natehorst240-sketch/HoboBalancer/BalancerREF/review/accel.png

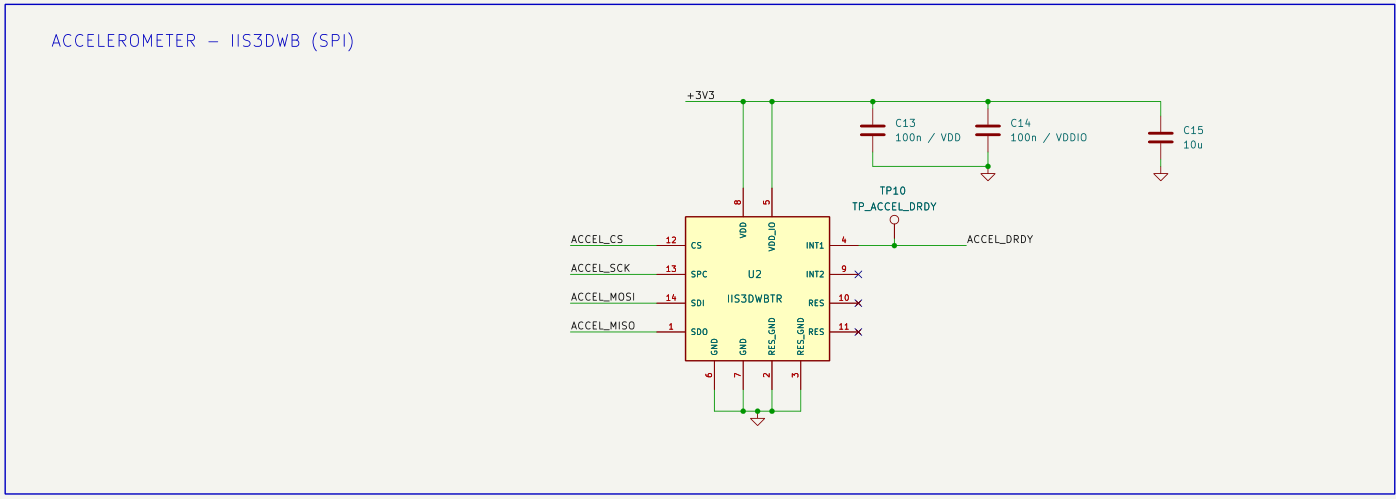
BalancerREF/review/accel.png
