natehorst240-sketch/HoboBalancer/BalancerREF/review/AO3401A-pinout.png

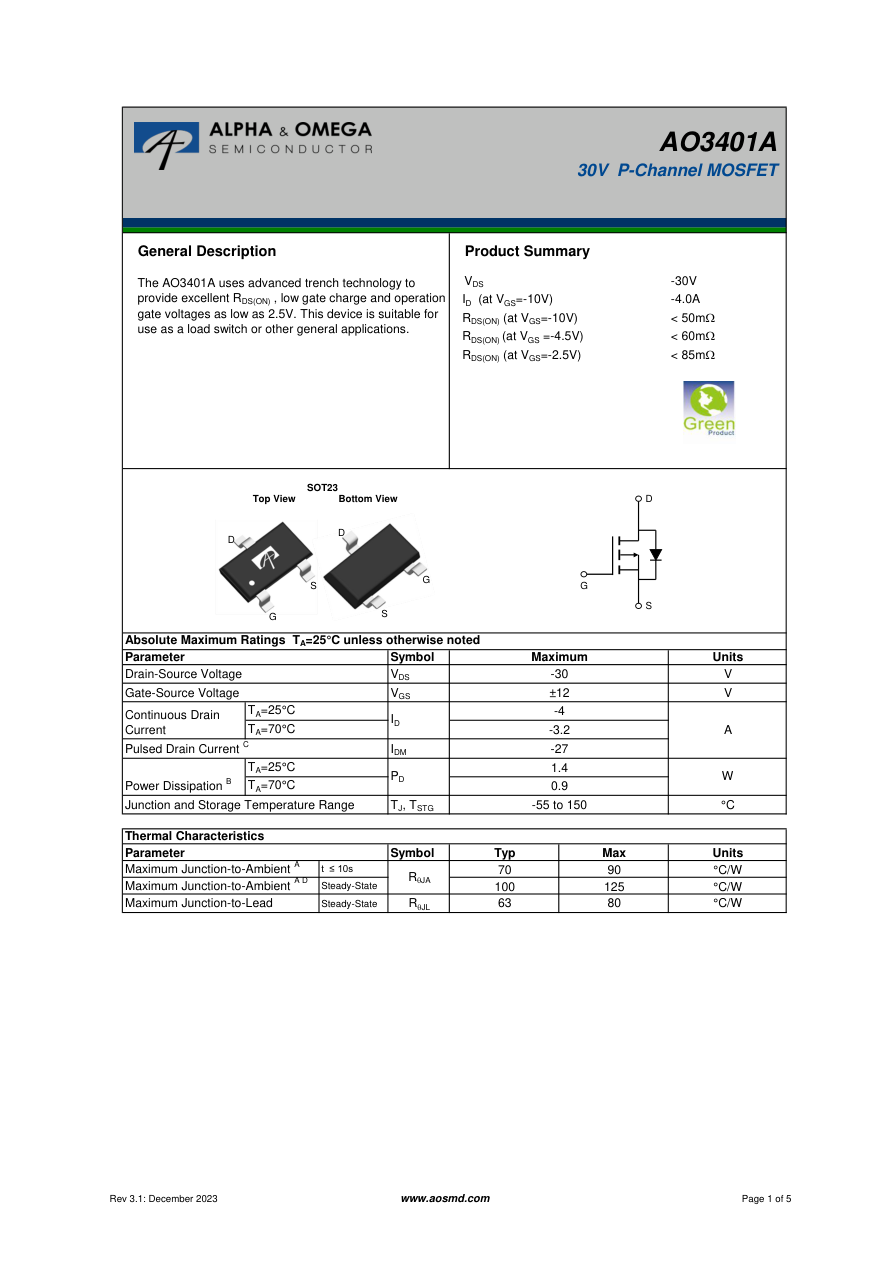
BalancerREF/review/AO3401A-pinout.png
