natehorst240-sketch/HoboBalancer/BalancerREF/review/lm1815-p1.png

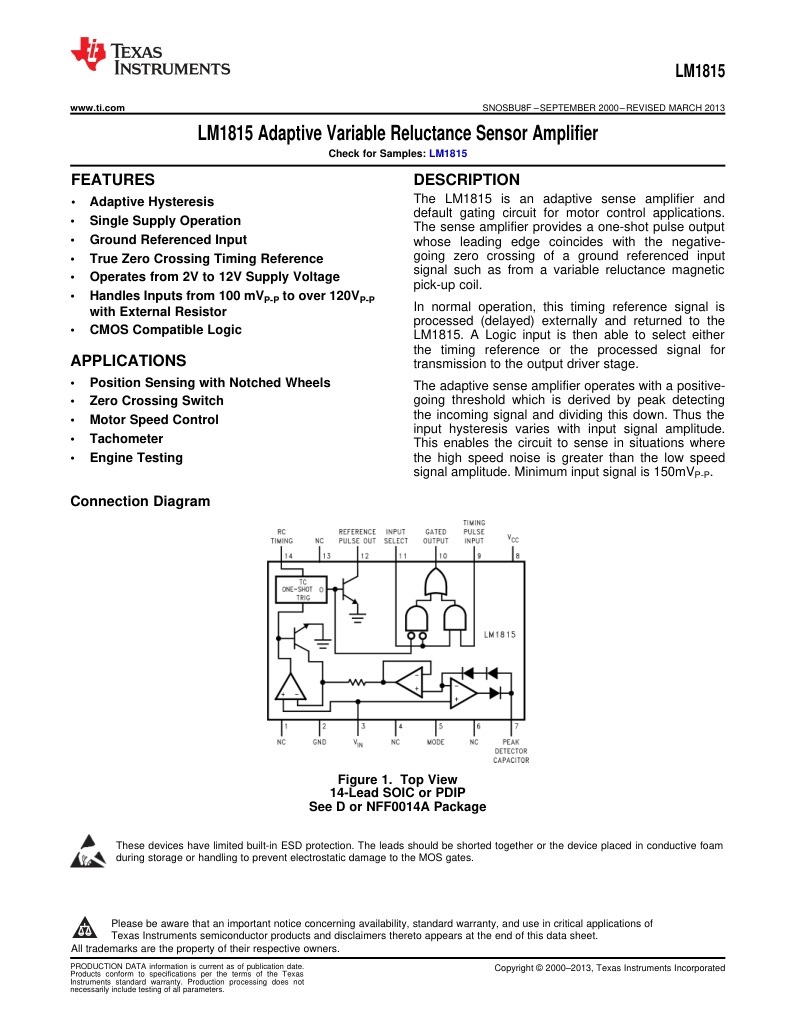
BalancerREF/review/lm1815-p1.png
