natehorst240-sketch/HoboBalancer/BalancerREF/review/lm1815-p6.png

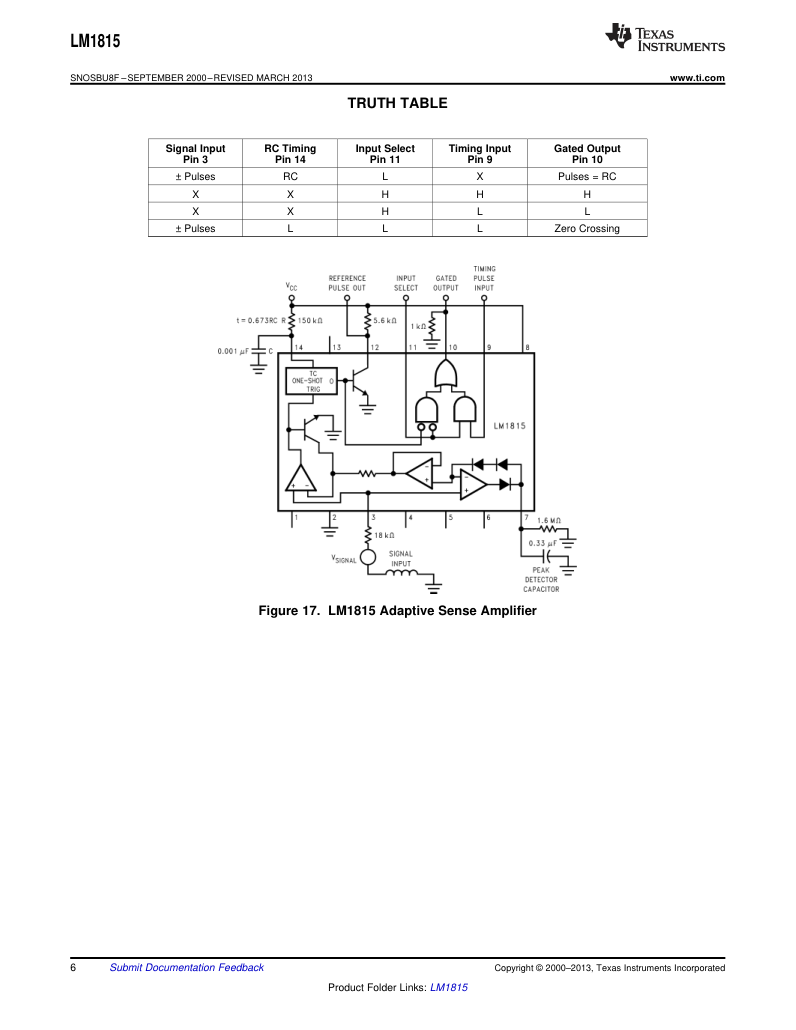
BalancerREF/review/lm1815-p6.png
