natehorst240-sketch/HoboBalancer/BalancerREF/review/mag.png

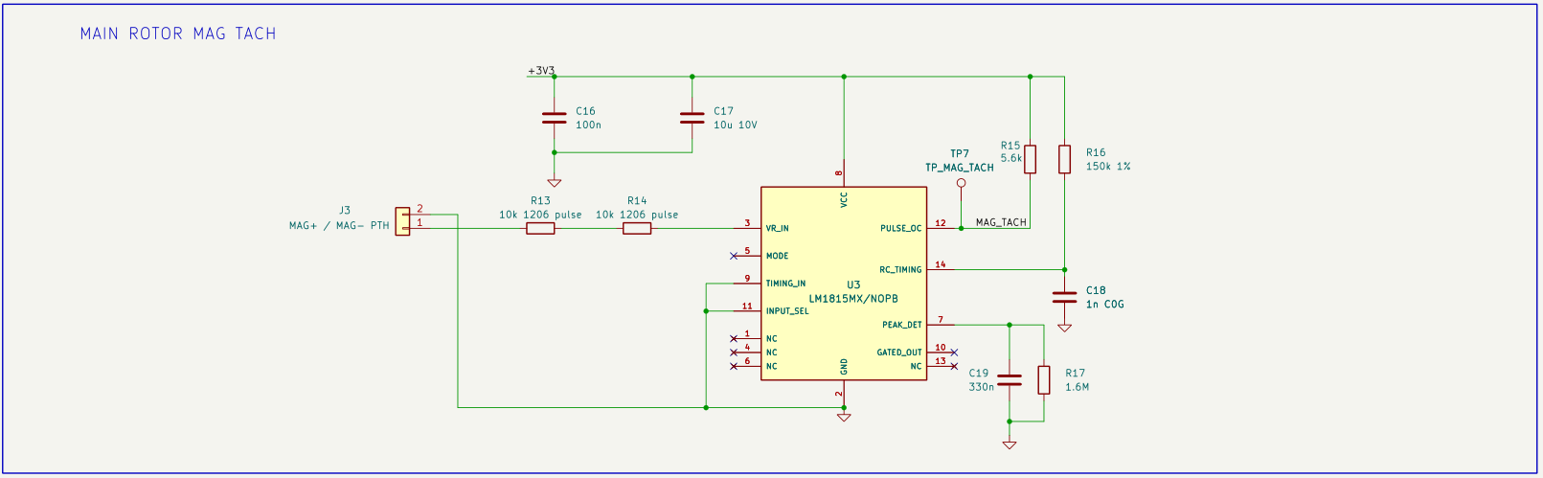
BalancerREF/review/mag.png
