natehorst240-sketch/HoboBalancer/BalancerREF/review/mcu.png

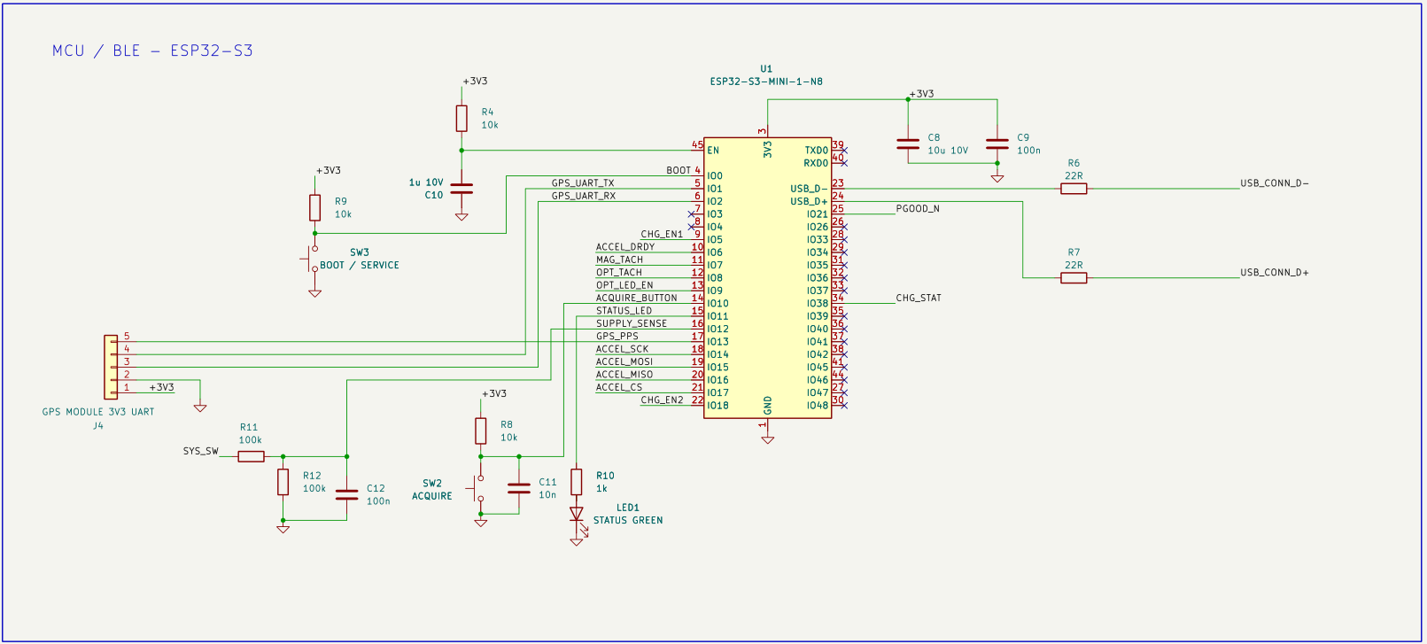
BalancerREF/review/mcu.png
