natehorst240-sketch/HoboBalancer/BalancerREF/review/notes-gps.png

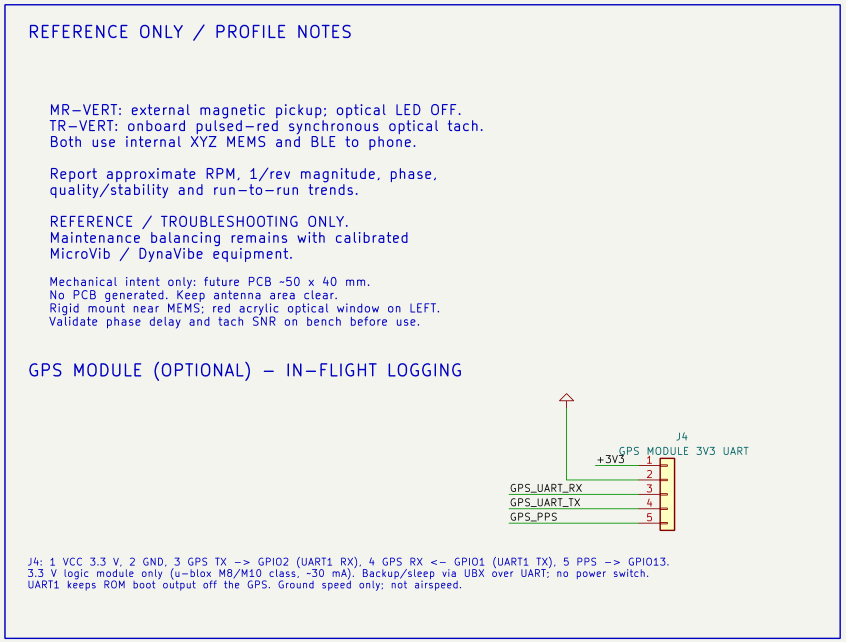
BalancerREF/review/notes-gps.png
