natehorst240-sketch/HoboBalancer/BalancerREF/review/opt-logic.png

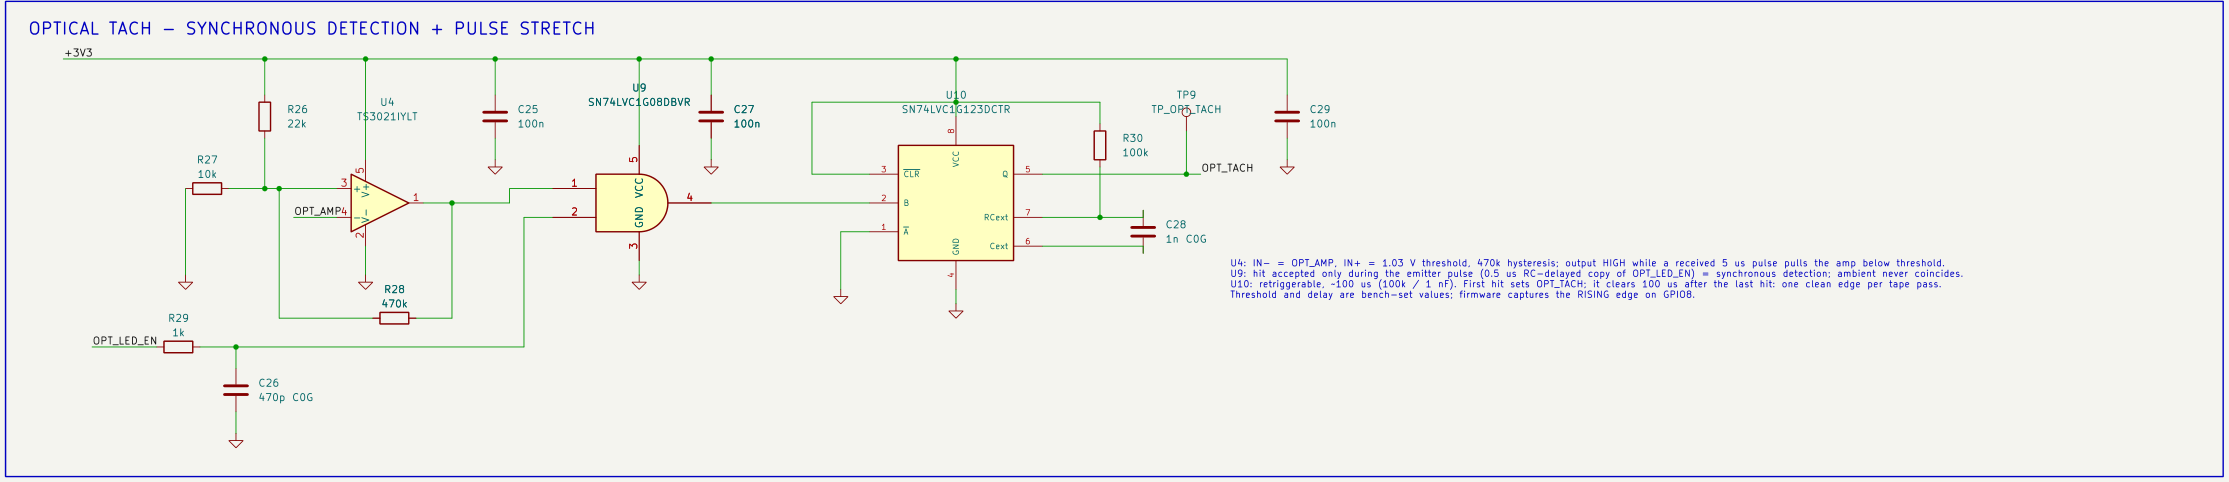
BalancerREF/review/opt-logic.png
