natehorst240-sketch/HoboBalancer/BalancerREF/review/opt.png

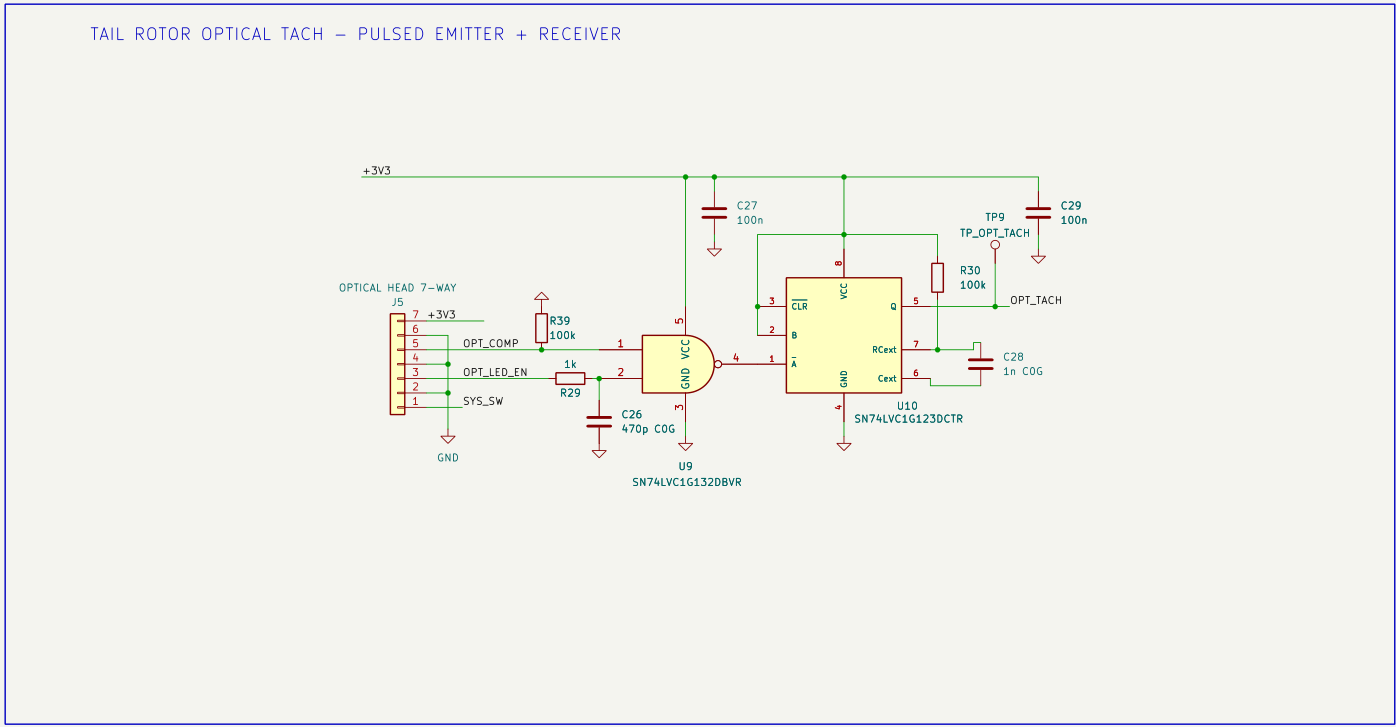
BalancerREF/review/opt.png
