natehorst240-sketch/HoboBalancer/BalancerREF/review/power-sharing.png

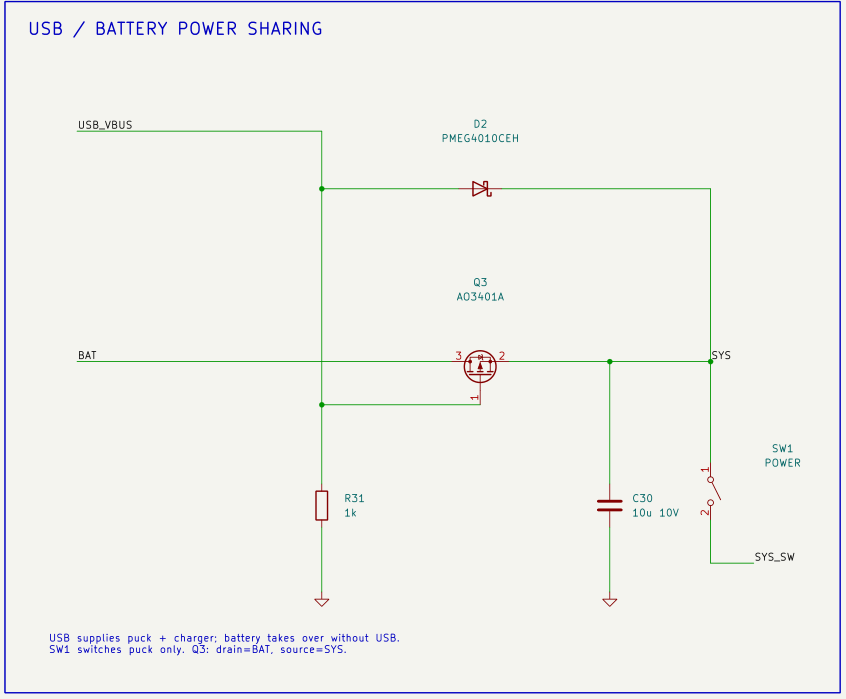
BalancerREF/review/power-sharing.png
