natehorst240-sketch/HoboBalancer/BalancerREF/review/power.png

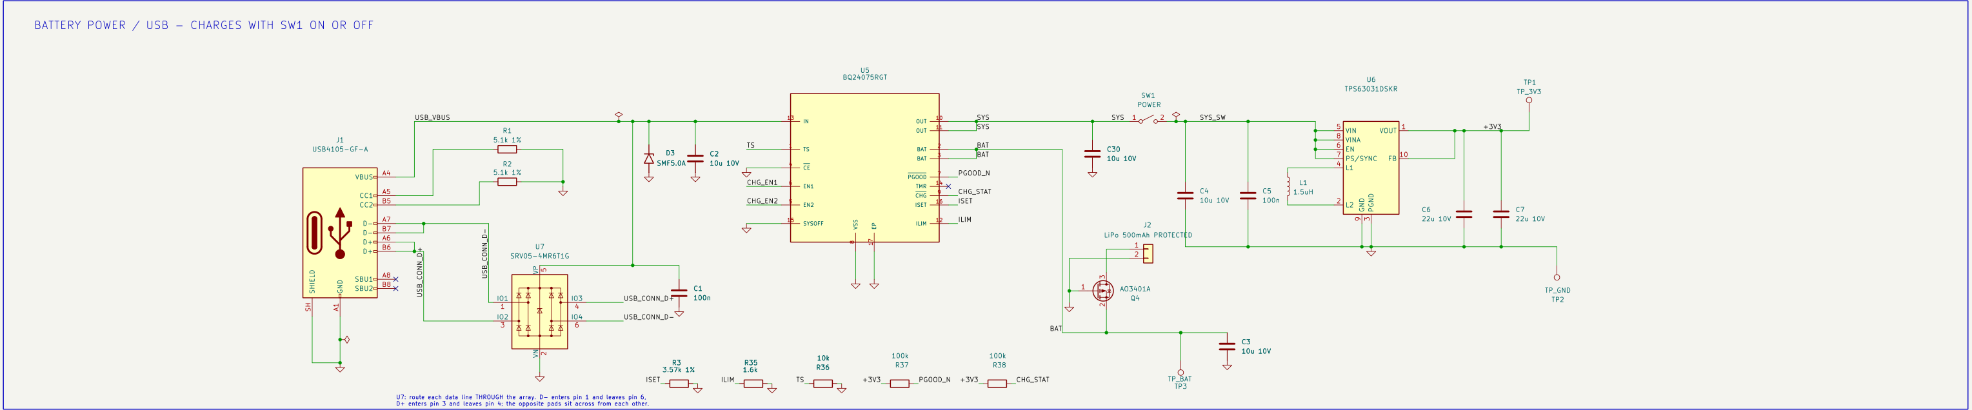
BalancerREF/review/power.png
