natehorst240-sketch/HoboBalancer/BalancerREF/review/reddit/board-head-top.png

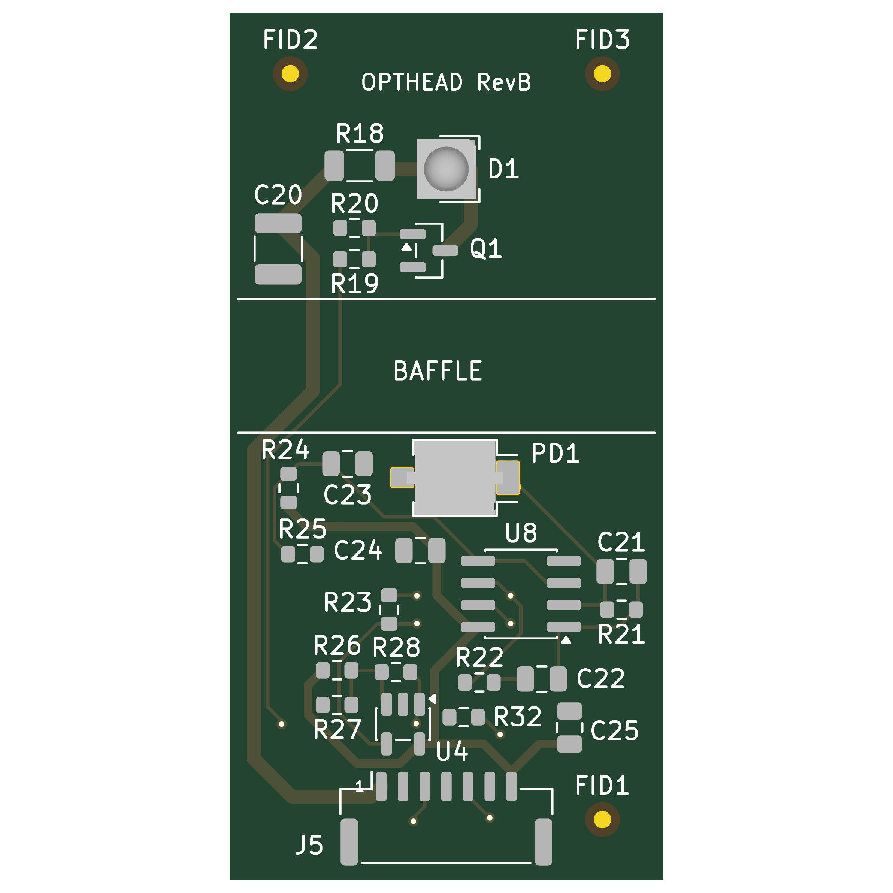
BalancerREF/review/reddit/board-head-top.png
