natehorst240-sketch/HoboBalancer/BalancerREF/review/reddit/board-main-bottom.png

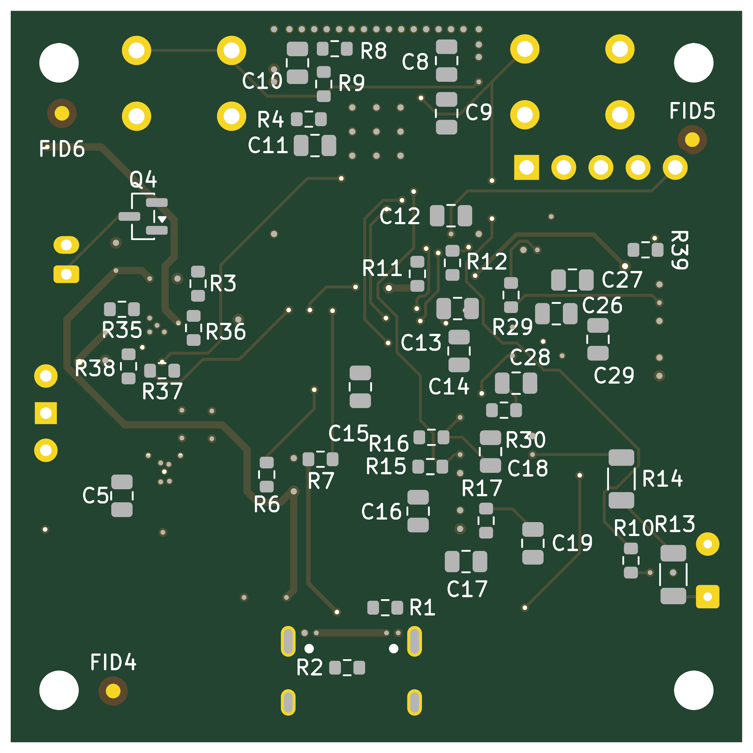
BalancerREF/review/reddit/board-main-bottom.png
