natehorst240-sketch/HoboBalancer/BalancerREF/review/reddit/board-main-top.png

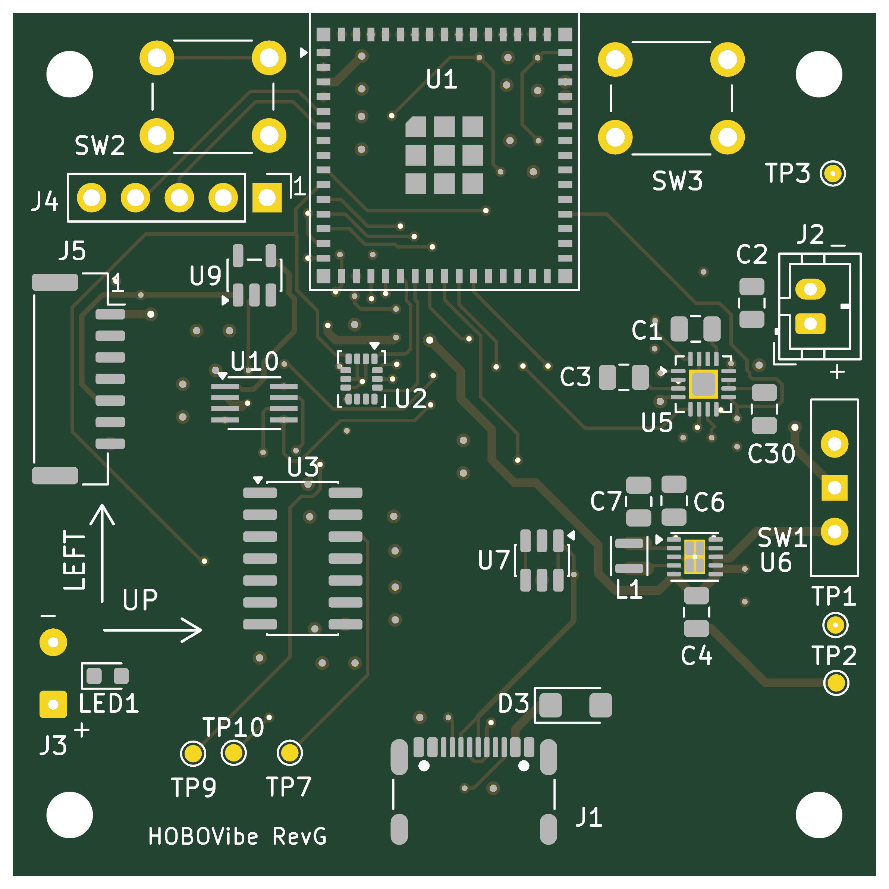
BalancerREF/review/reddit/board-main-top.png
