natehorst240-sketch/HoboBalancer/BalancerREF/review/reg.png

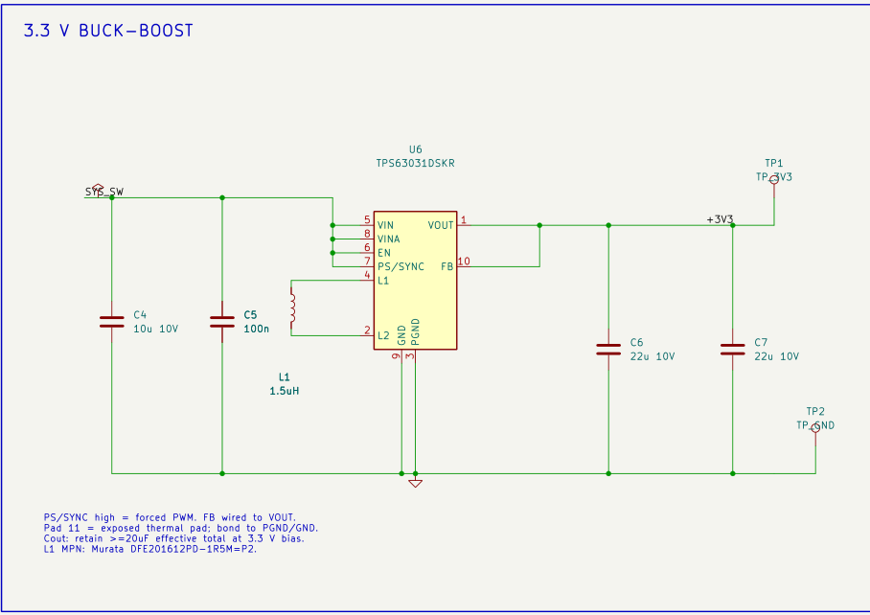
BalancerREF/review/reg.png
