natehorst240-sketch/HoboBalancer/BalancerREF/review/ui.png

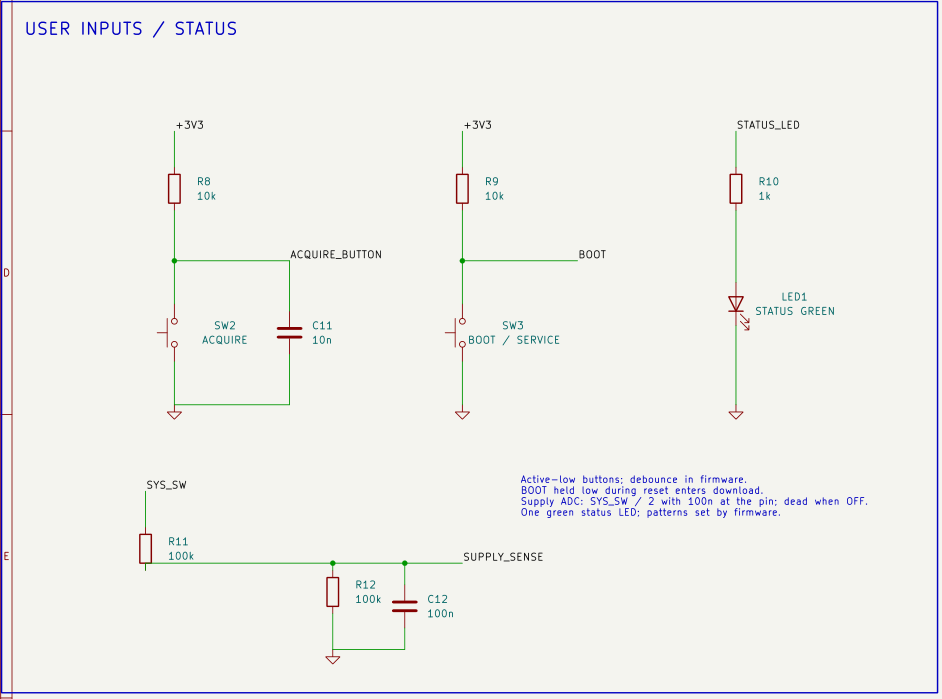
BalancerREF/review/ui.png
