natehorst240-sketch/HoboBalancer/BalancerREF/BalancerREF-Schematic-RevD.pdf

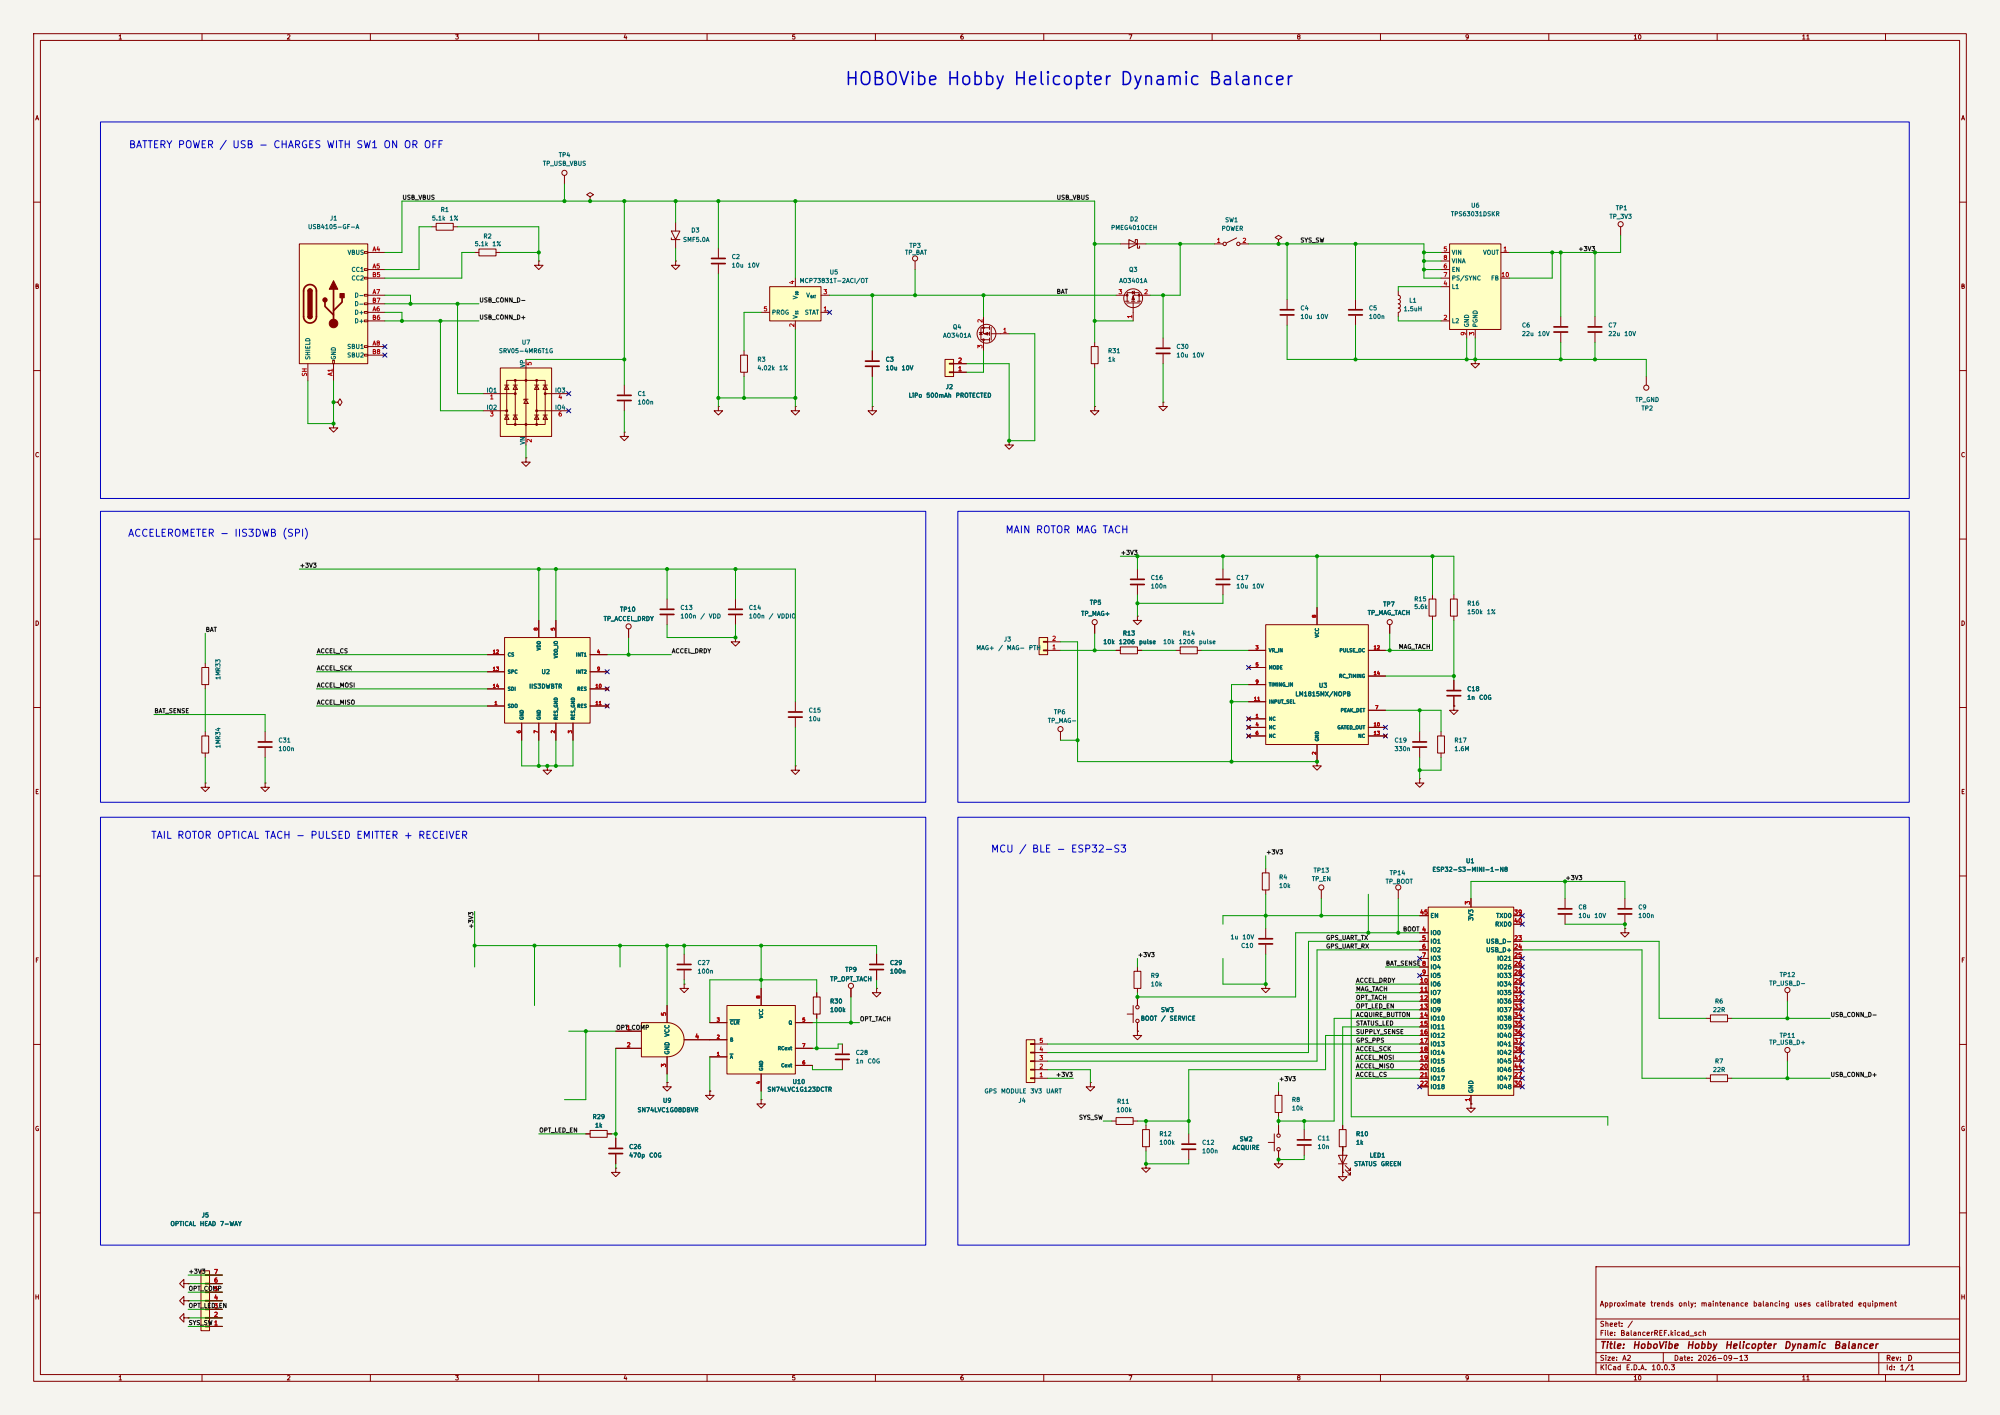
[picture p27: page 1]

BATTERY POWER / USB - CHARGES WITH SW1 ON OR OFF

+3V3 MAIN ROTOR MAG TACH

TAIL ROTOR OPTICAL TACH - PULSED EMITTER + RECEIVER

6 6 | 23 USB_D+ 23 USB_D+ 24 24

OPT_COMP

SUPPLY_SENSE 16 16
GPS_PPS 17 17

4 | | | ACCEL_SCK 18 18

Approximate trends only; maintenance balancing uses calibrated equipment

Sheet: /
File: BalancerREF.kicad_sch
Title: HoboVibe Hobby Helicopter Dynamic Balancer

Size: A2 | Rev: D
KiCad E.D.A. 10.0.3 | Id: 1/1
