natehorst240-sketch/HoboBalancer/BalancerREF/BalancerREF-Schematic-RevB.pdf

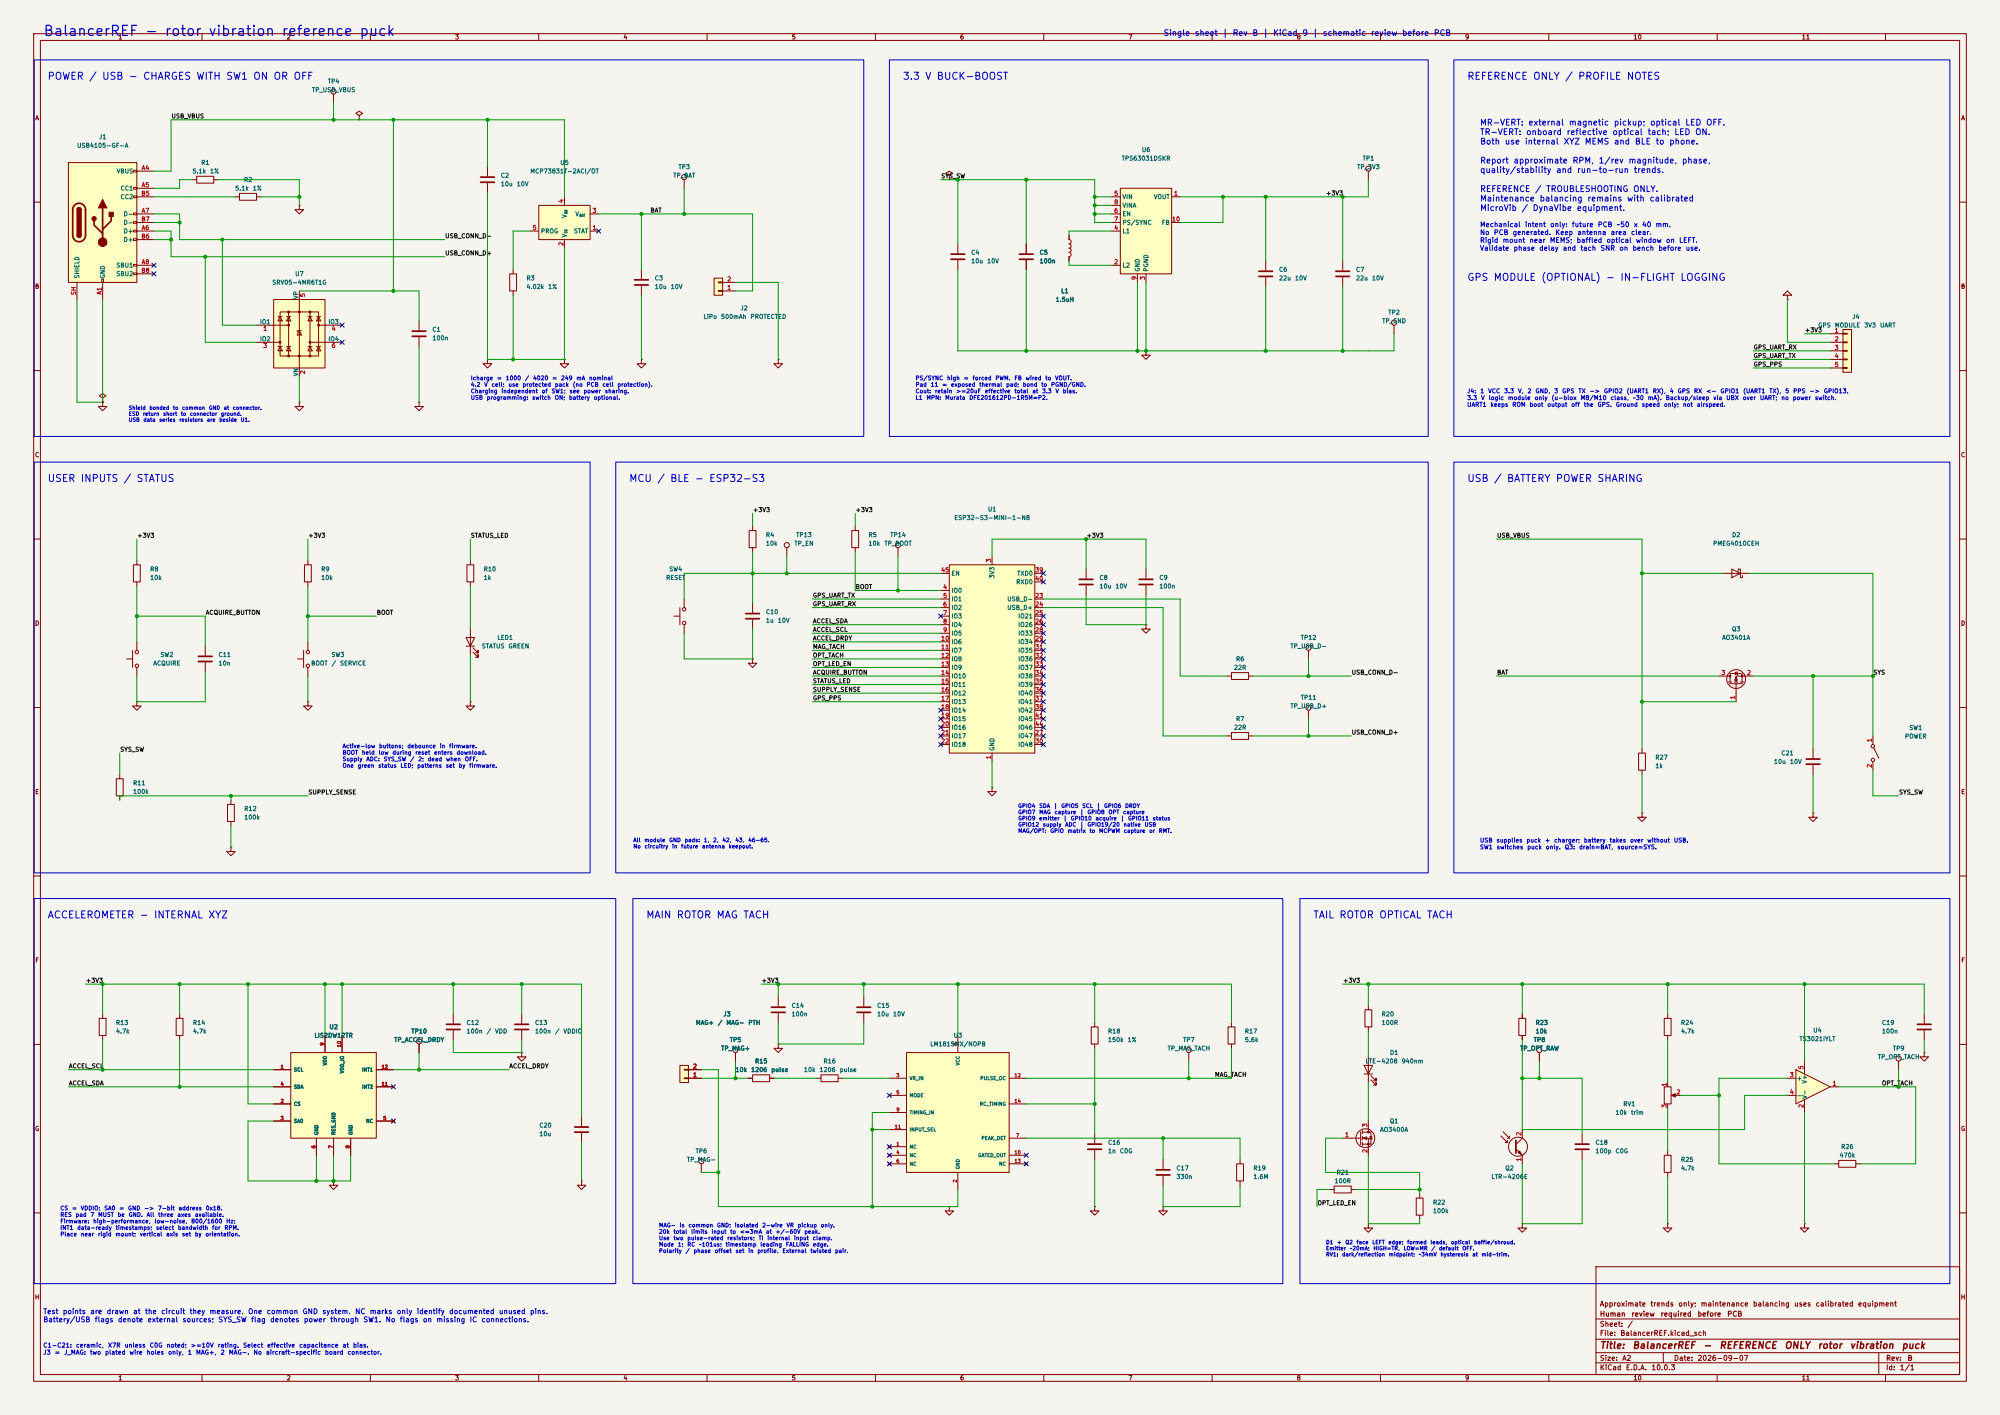
[picture p28: page 1]

BalancerREF - rotor vibration reference puck

Single sheet | Rev B | KiCad 9 | schematic review before PCB

POWER / USB - CHARGES WITH SW1 ON OR OFF

Validate phase delay and tach SNR on bench before use. MR-VERT: external magnetic pickup; optical LED OFF.
TR-VERT: onboard reflective optical tach; LED ON.
Both use internal XYZ MEMS and BLE to phone.

Report approximate RPM, 1/rev magnitude, phase,
quality/stability and run-to-run trends.

REFERENCE / TROUBLESHOOTING ONLY.
Maintenance balancing remains with calibrated
MicroVib / DynaVibe equipment.

Mechanical intent only: future PCB ~50 x 40 mm. No PCB generated. Keep antenna area clear.

Rigid mount near MEMS; baffled optical window on LEFT.

GPS MODULE (OPTIONAL) - IN-FLIGHT LOGGING

Icharge = 1000 / 4020 = 249 mA nominal 4.2 V cell; use protected pack (no PCB cell protection).

Charging independent of SW1; see power sharing. USB programming: switch ON; battery optional.

GPIO4 SDA | GPIO5 SCL | GPIO6 DRDY GPIO7 MAG capture | GPIO8 OPT capture GPIO9 emitter | GPIO10 acquire | GPIO11 status GPIO12 supply ADC | GPIO19/20 native USB MAG/OPT: GPIO matrix to MCPWM capture or RMT.

USB supplies puck + charger; battery takes over without USB. SW1 switches puck only. Q3: drain=BAT, source=SYS. CS = VDDIO; SA0 = GND -> 7-bit address 0x18. RES pad 7 MUST be GND. All three axes available. Firmware: high-performance, low-noise, 800/1600 Hz;

All module GND pads: 1, 2, 42, 43, 46-65. No circuitry in future antenna keepout.

MAG- is common GND; isolated 2-wire VR pickup only. 20k total limits input to <=3mA at +/-60V peak. Use two pulse-rated resistors; TI internal input clamp. Mode 1; RC ~101us; timestamp leading FALLING edge.

D1 + Q2 face LEFT edge; formed leads, optical baffle/shroud. Emitter ~20mA; HIGH=TR, LOW=MR / default OFF. RV1: dark/reflection midpoint; ~34mV hysteresis at mid-trim.

Polarity / phase offset set in profile. External twisted pair.

Approximate trends only; maintenance balancing uses calibrated equipment
Human review required before PCB
Sheet: /
File: BalancerREF.kicad_sch
Title: BalancerREF - REFERENCE ONLY rotor vibration puck

Test points are drawn at the circuit they measure. One common GND system. NC marks only identify documented unused pins.
Battery/USB flags denote external sources; SYS_SW flag denotes power through SW1. No flags on missing IC connections.

Size: A2 | Rev: B
KiCad E.D.A. 10.0.3 | Id: 1/1
