natehorst240-sketch/HoboBalancer/BalancerCarrier/firmware/tests/check_pinmap.py

"""Check BalancerCarrier firmware GPIO assignments against the KiCad schematic.

Run: python BalancerCarrier/firmware/tests/check_pinmap.py

Differences from BalancerREF's version, both deliberate:

  Source of truth. BalancerREF's test reads review/IC-pin-audit.csv and says so in its
  own docstring: "this test is only as current as the last run of that". A generated
  CSV that nobody re-runs is not a guard. This reads BalancerCarrier.net, exported
  straight from the schematic, and REFUSES TO PASS if the .kicad_sch is newer - so
  staleness fails loudly instead of quietly certifying an old layout.

  Constraint checks. Matching net names is not enough. MAG_TACH sat on GPIO33 from the
  FeatherS3[D] swap until 2026-09-21: the net name matched, pulse capture worked, and
  EXT1 rotor-spin wake silently could not arm, because GPIO33 is outside the ESP32-S3's
  22 RTC GPIOs. A name-only check would have passed that. So this also asserts the
  electrical constraints each signal actually depends on.
"""
from pathlib import Path
import re
import sys

ROOT = Path(__file__).resolve().parents[2]          # BalancerCarrier/
SCH = ROOT / 'BalancerCarrier.kicad_sch'
NET = ROOT / 'BalancerCarrier.net'
HPP = ROOT / 'firmware/src/board.hpp'

# ESP32-S3 facts, from the datasheet and CONFIG_SOC_RTCIO_PIN_COUNT
RTC_GPIO = range(0, 22)      # EXT1 deep-sleep wake is only possible on these
ADC1_GPIO = range(1, 11)     # ADC2 is unusable while Wi-Fi is up
RESERVED = {0: 'module boot button', 3: 'strapping pin', 43: 'UART0 console',
            44: 'UART0 console'}

# firmware name -> (schematic net, constraints it depends on)
EXPECTED = {
    'drdy':      ('ACCEL_DRDY', set()),
    'mag':       ('MAG_TACH', {'rtc'}),          # EXT1 wake: rotor spin-up
    'opt':       ('OPT_TACH', set()),
    'emitter':   ('OPT_LED_EN', set()),
    'acquire':   ('ACQUIRE_BUTTON', {'rtc'}),    # EXT1 wake: button press
    'led':       ('STATUS_LED', set()),
    'gpsTx':     ('GPS_UART_TX', set()),
    'gpsRx':     ('GPS_UART_RX', set()),
    'gpsPps':    ('GPS_PPS', set()),
    'accelSck':  ('ACCEL_SCK', set()),
    'accelMosi': ('ACCEL_MOSI', set()),
    'accelMiso': ('ACCEL_MISO', set()),
    'accelCs':   ('ACCEL_CS', set()),
}

# Fixed by the FeatherS3[D] itself, so they are in no carrier netlist and cannot be
# checked against the schematic. Values from unexpectedmaker/esp32s3 - the MicroPython
# helper gives LDO2 = const(39) and VBUS_SENSE = const(34); the I2C pins are the
# module's own bus, carrying the MAX17048 and the STEMMA QT connector. Checked here so
# a typo still fails rather than silently driving the wrong pin.
MODULE_INTERNAL = {'ldo2': 39, 'vbusSense': 34, 'i2cSda': 8, 'i2cScl': 9}


def fail(msg):
    print('FAIL: ' + msg)
    sys.exit(1)


if not NET.exists():
    fail(f'{NET.name} is missing. Export it with:\n'
         f'  kicad-cli sch export netlist --format kicadsexpr -o {NET.name} {SCH.name}')
if SCH.stat().st_mtime > NET.stat().st_mtime:
    fail(f'{SCH.name} is newer than {NET.name}; the netlist is stale. Re-export it with:\n'
         f'  kicad-cli sch export netlist --format kicadsexpr -o {NET.name} {SCH.name}')

# ---- what the schematic says: U1 GPIO number -> net name --------------------
text = NET.read_text(encoding='utf8')
nets = re.findall(r'\(net\b.*?\(name "([^"]*)"\)(.*?)(?=\n\t\t\(net\b|\n\t\)\n)', text, re.S)
if not nets:
    fail('could not parse any nets out of the netlist')
sch_gpio = {}
for name, body in nets:
    for ref, pin, fn in re.findall(
            r'\(ref "([^"]+)"\)\s*\(pin "([^"]+)"\)\s*\(pinfunction "([^"]+)"\)', body):
        if ref != 'U1':
            continue
        m = re.match(r'IO(\d+)(?:_\d+)?$', fn)
        if m:
            sch_gpio[int(m.group(1))] = name.lstrip('/')

# ---- what firmware says: name -> GPIO number -------------------------------
decls = ';'.join(re.findall(r'^\s*constexpr\s+int\s+([^;]*);', HPP.read_text(encoding='utf8'), re.M))
pins = {k: int(v) for k, v in re.findall(r'\b(\w+)=(\d+)', decls)}
if not pins:
    fail('no constexpr pin declarations found in board.hpp')

problems = []
for name, (signal, needs) in EXPECTED.items():
    if name not in pins:
        problems.append(f'{name}: declared nowhere in board.hpp')
        continue
    g = pins[name]
    actual = sch_gpio.get(g)
    if actual is None:
        problems.append(f'{name}=GPIO{g}: the schematic has no U1 pin for that GPIO')
    elif actual.startswith('unconnected-'):
        problems.append(f'{name}=GPIO{g}: that pin is a no-connect in the schematic')
    elif actual != signal:
        problems.append(f'{name}=GPIO{g}: schematic has {actual!r}, expected {signal!r}')
    if g in RESERVED:
        problems.append(f'{name}=GPIO{g}: reserved - {RESERVED[g]}')
    if g in (MODULE_INTERNAL['i2cSda'], MODULE_INTERNAL['i2cScl']):
        problems.append(f'{name}=GPIO{g}: that is the module I2C bus (MAX17048 / STEMMA QT)')
    if 'rtc' in needs and g not in RTC_GPIO:
        problems.append(f'{name}=GPIO{g}: EXT1 deep-sleep wake needs an RTC GPIO (0-21)')
    if 'adc1' in needs and g not in ADC1_GPIO:
        problems.append(f'{name}=GPIO{g}: needs ADC1 (GPIO1-10); ADC2 is dead with Wi-Fi up')

for name, want in MODULE_INTERNAL.items():
    if name not in pins:
        problems.append(f'{name}: declared nowhere in board.hpp')
    elif pins[name] != want:
        problems.append(f'{name}=GPIO{pins[name]}: the FeatherS3[D] fixes this at GPIO{want}')

# the silent-gap case: a pin added to board.hpp but never checked here
uncovered = sorted(set(pins) - set(EXPECTED) - set(MODULE_INTERNAL))
if uncovered:
    problems.append(f'board.hpp pins not covered by this test: {uncovered}')

if problems:
    print(f'FAIL: {len(problems)} problem(s)')
    for p in problems:
        print('  - ' + p)
    sys.exit(1)

wake = [f'{n}=GPIO{pins[n]}' for n, (_, c) in EXPECTED.items() if 'rtc' in c]
print(f'PASS: {len(EXPECTED)} header signals match the schematic netlist, '
      f'{len(MODULE_INTERNAL)} module-internal pins match the FeatherS3[D]; '
      f'all {len(pins)} board.hpp pins covered.')
print(f'      EXT1 wake sources all on RTC GPIO: {", ".join(wake)}')
